avamurrayprojects/Autonomous-Platooning-System-for-Model-Car/hardware/STL/mounts/servo-mount.stl

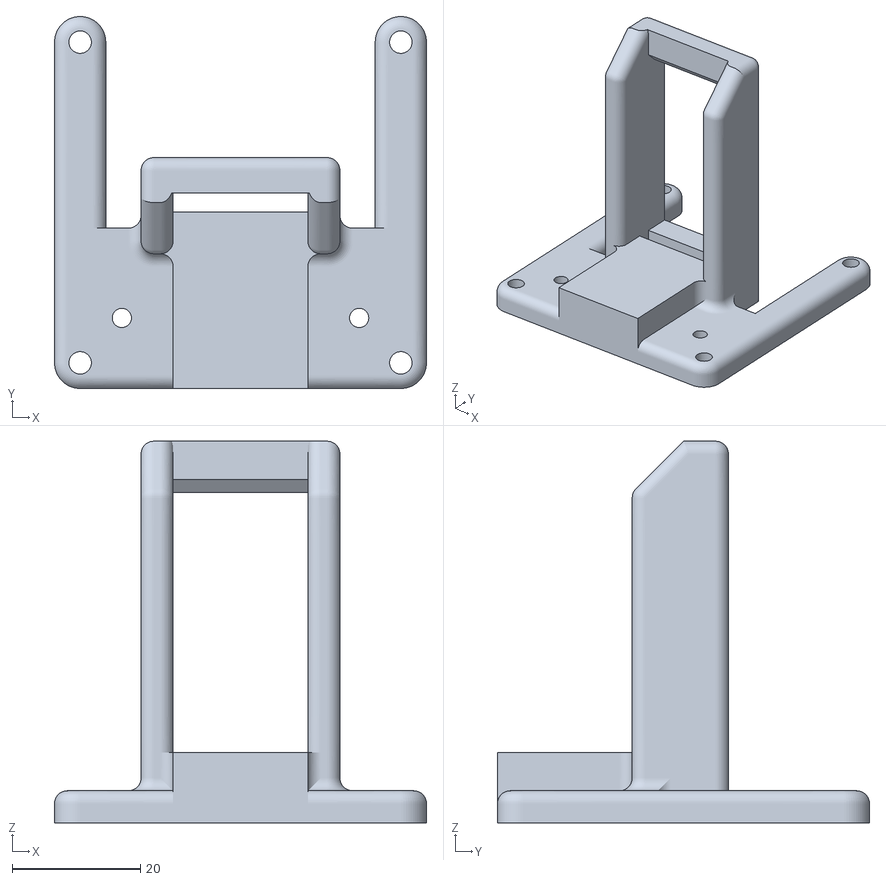
[picture p16: CAD file, 2025-04-11]
hardware/STL/mounts/servo-mount.stl
58.0 x 58.0 x 59.5
